alexabulgaru/E-Book-Reader-TSC/Images/Baterie_1.jpeg

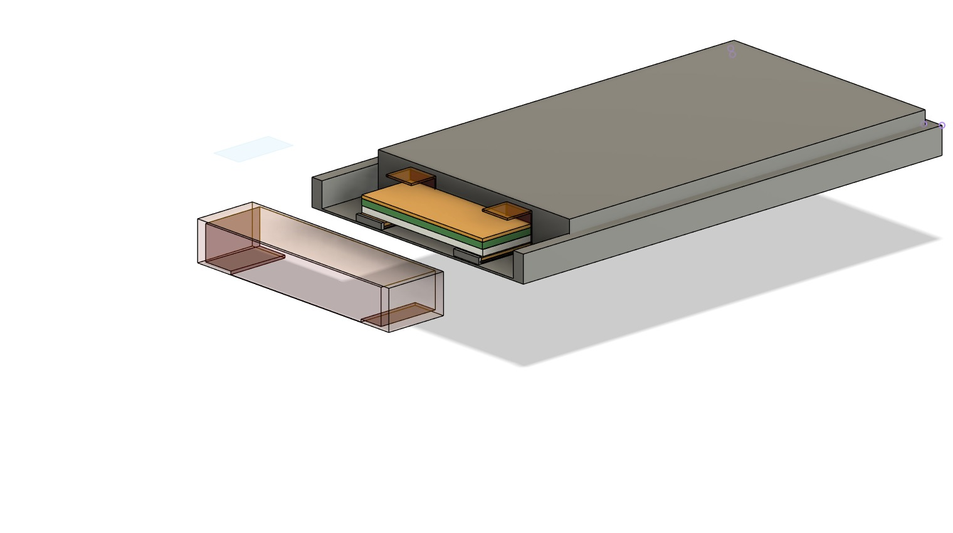
Images/Baterie_1.jpeg
