alexabulgaru/E-Book-Reader-TSC/Images/Baterie_2.jpeg

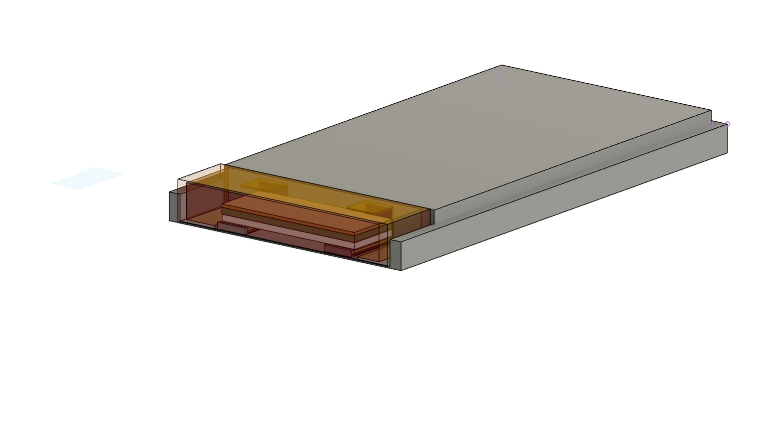
Images/Baterie_2.jpeg
