alexabulgaru/E-Book-Reader-TSC/Images/Display_2.jpeg

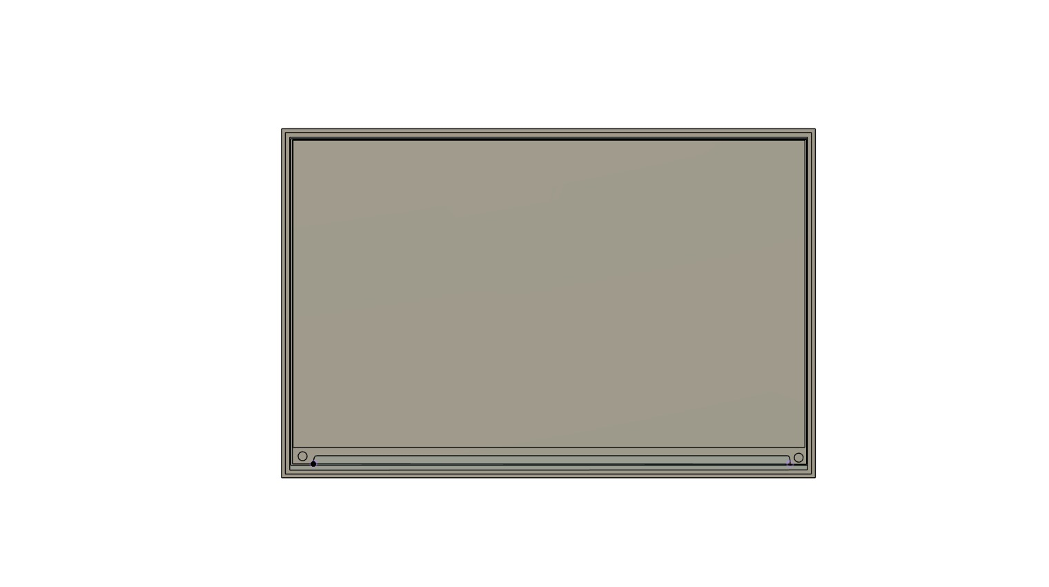
Images/Display_2.jpeg
