alexabulgaru/E-Book-Reader-TSC/Images/Dispozitiv_2.jpeg

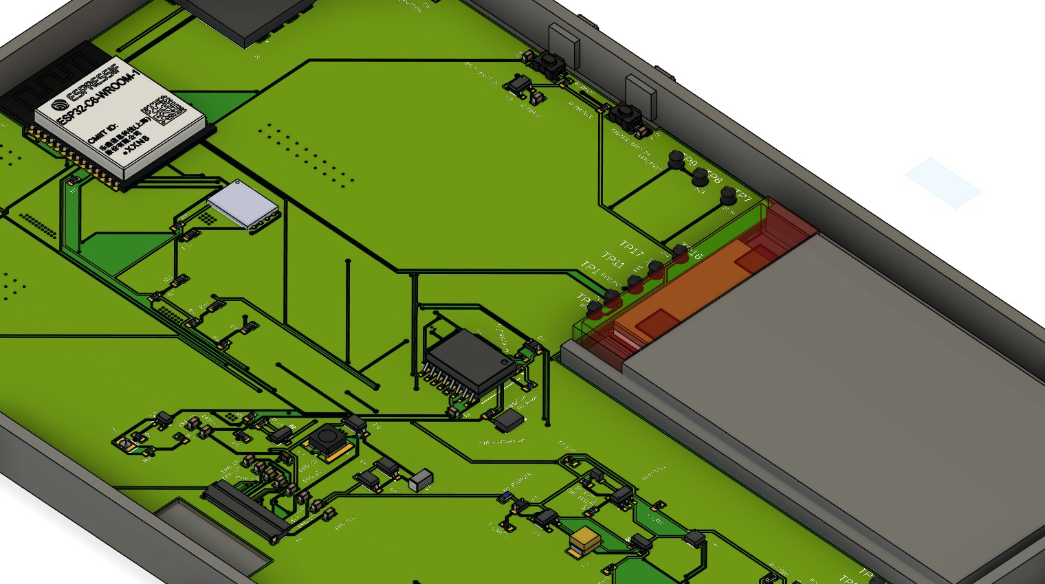
Images/Dispozitiv_2.jpeg
