alexabulgaru/E-Book-Reader-TSC/Images/Dispozitiv_3.jpeg

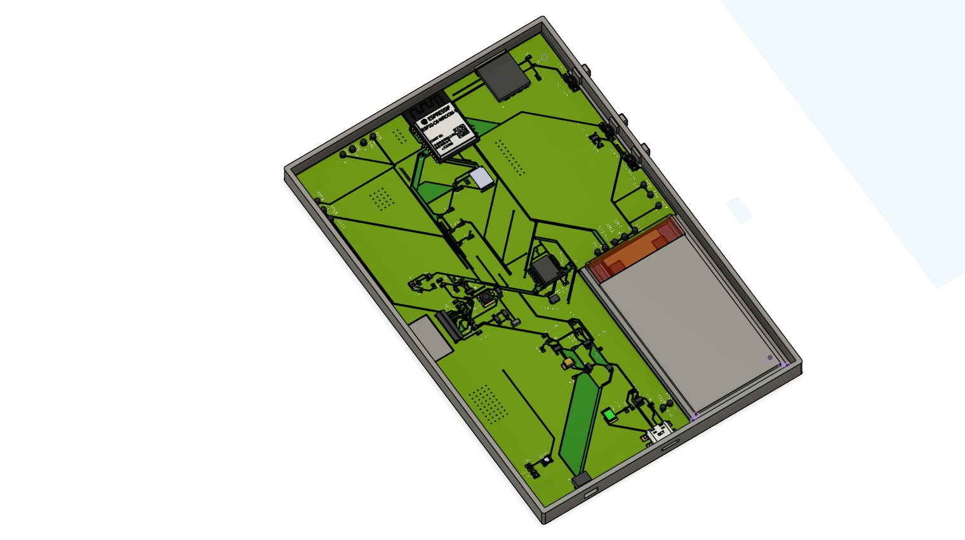
Images/Dispozitiv_3.jpeg
