alexabulgaru/E-Book-Reader-TSC/Images/Placuta_1.jpeg

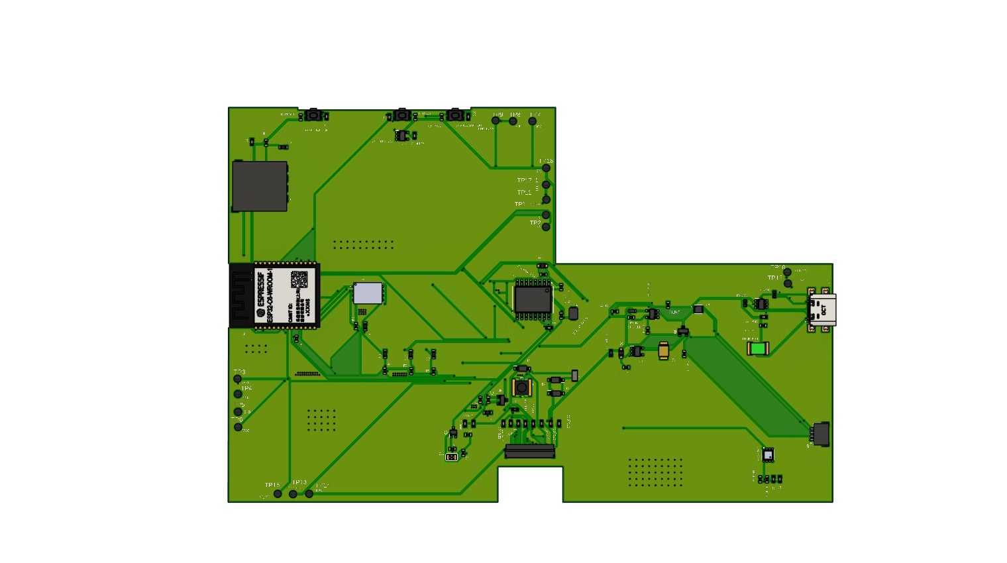
Images/Placuta_1.jpeg
